DRubioG/Zynq-eame/Documentacion/img1.png

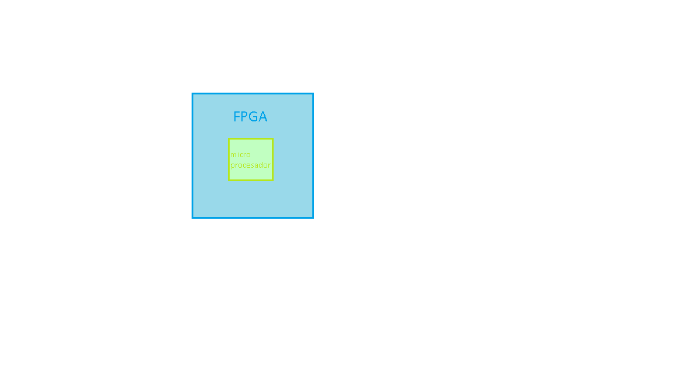
Documentacion/img1.png
