DRubioG/Zynq-eame/Zynq-eame_1/KiCad/imagenes/CLG400.PNG

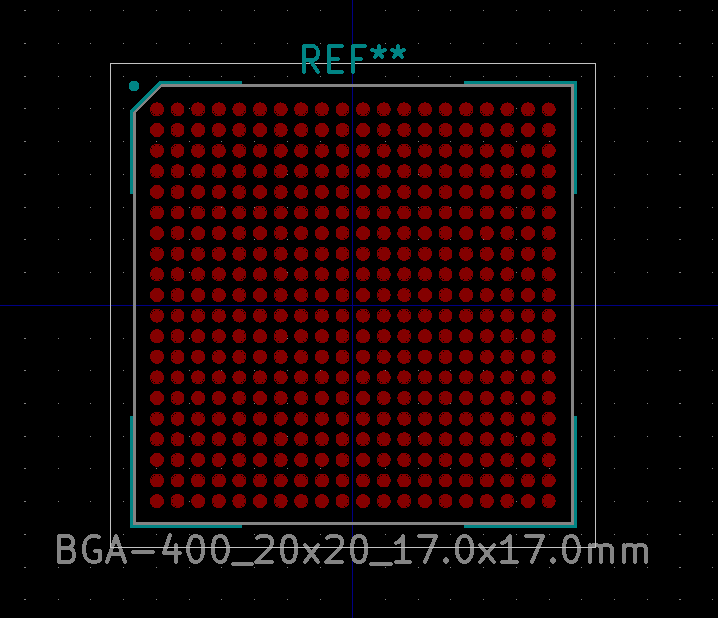
Zynq-eame_1/KiCad/imagenes/CLG400.PNG
