DRubioG/Zynq-eame/Zynq-eame_1/KiCad/imagenes/XC7Z010-U1I.PNG

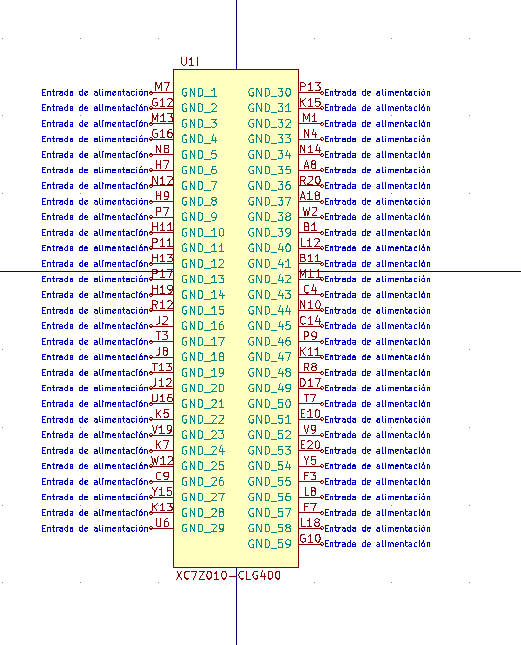
Zynq-eame_1/KiCad/imagenes/XC7Z010-U1I.PNG
