DRubioG/Zynq-eame/Zynq-eame_1/Vivado/Zynq-eame/1.5/Zynq-eame_0.jpg

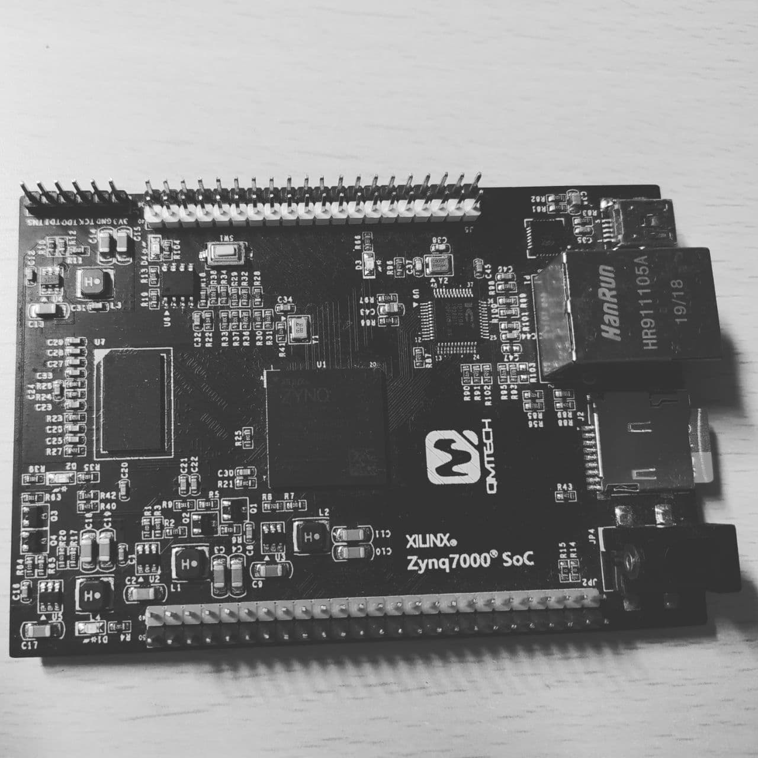
Zynq-eame_1/Vivado/Zynq-eame/1.5/Zynq-eame_0.jpg
